willumpie82/ledleafs/CAD/images/0.jpg

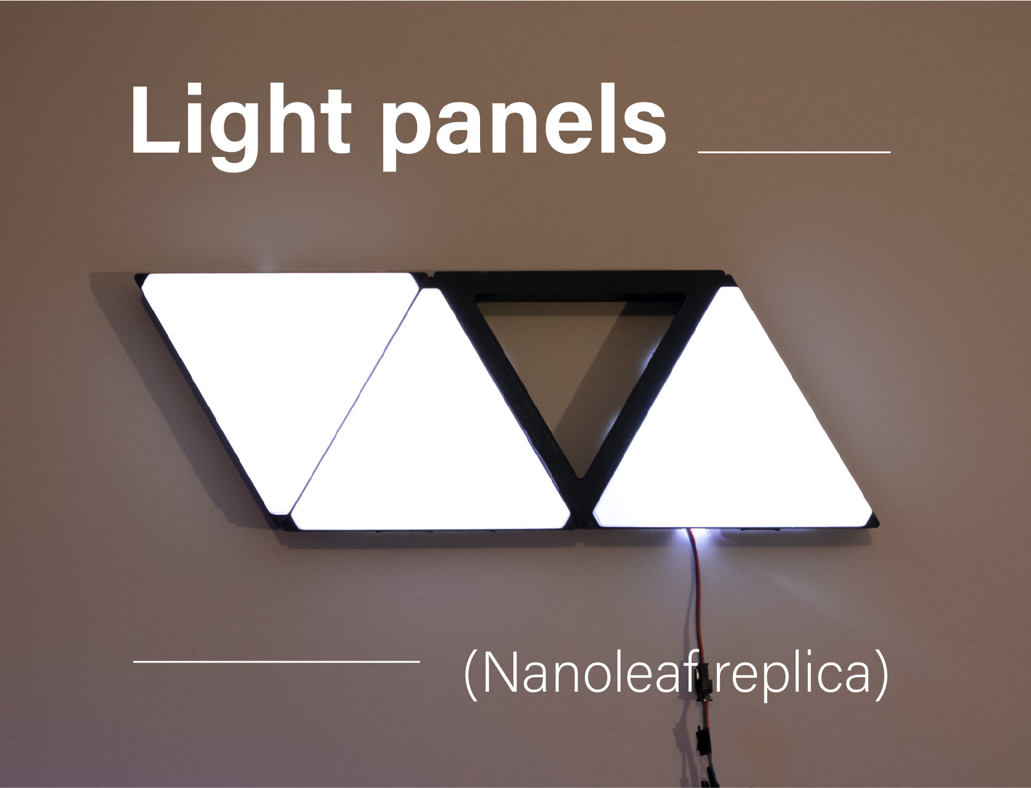
CAD/images/0.jpg
