willumpie82/ledleafs/CAD/images/Manuel_2.jpg

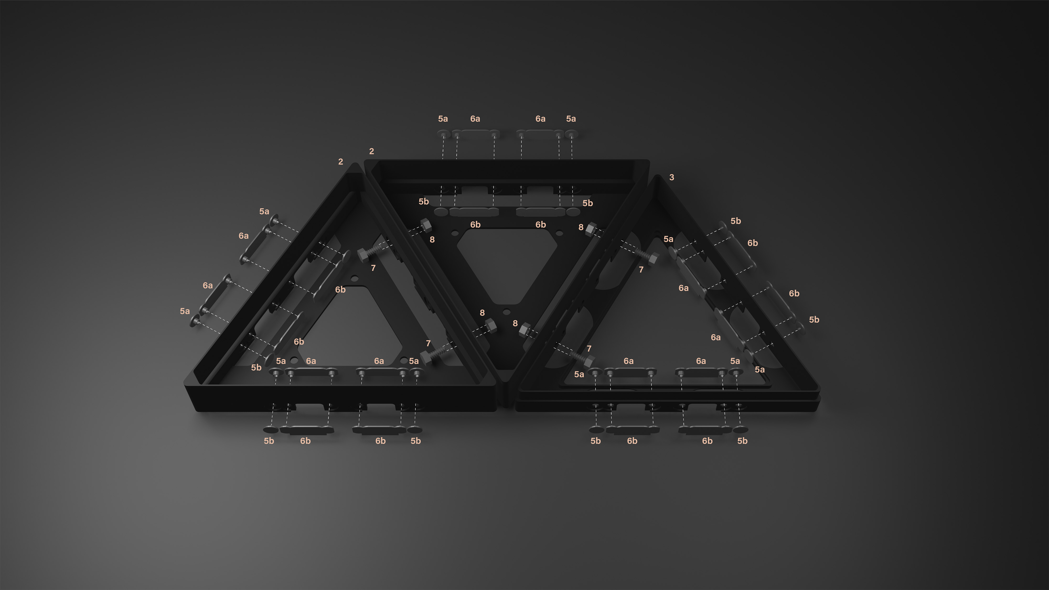
CAD/images/Manuel_2.jpg
