willumpie82/ledleafs/CAD/images/Manuel_5.jpg

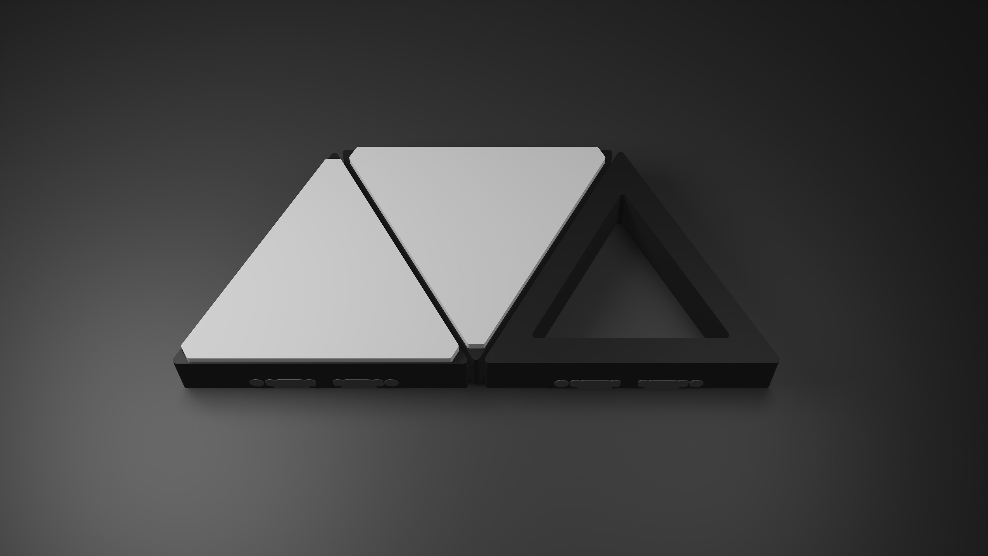
CAD/images/Manuel_5.jpg
