willumpie82/ledleafs/CAD/images/Manuel_6.jpg

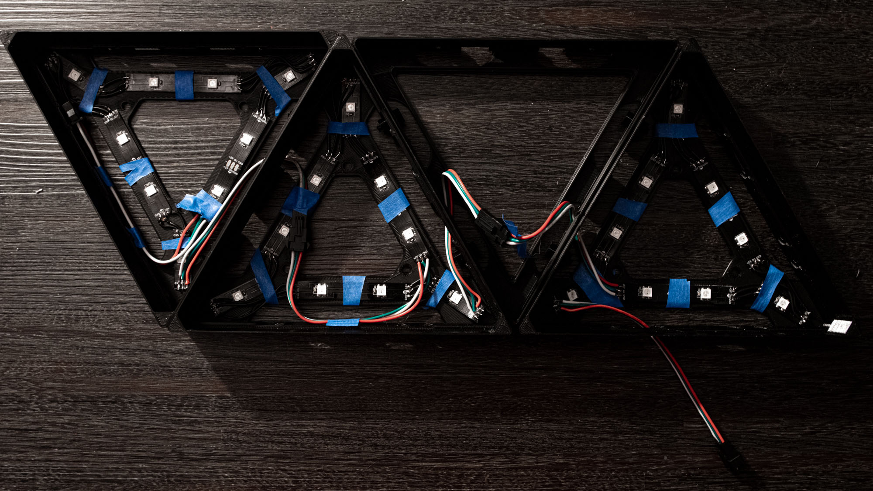
CAD/images/Manuel_6.jpg
