willumpie82/ledleafs/CAD/images/Manuel_8.jpg

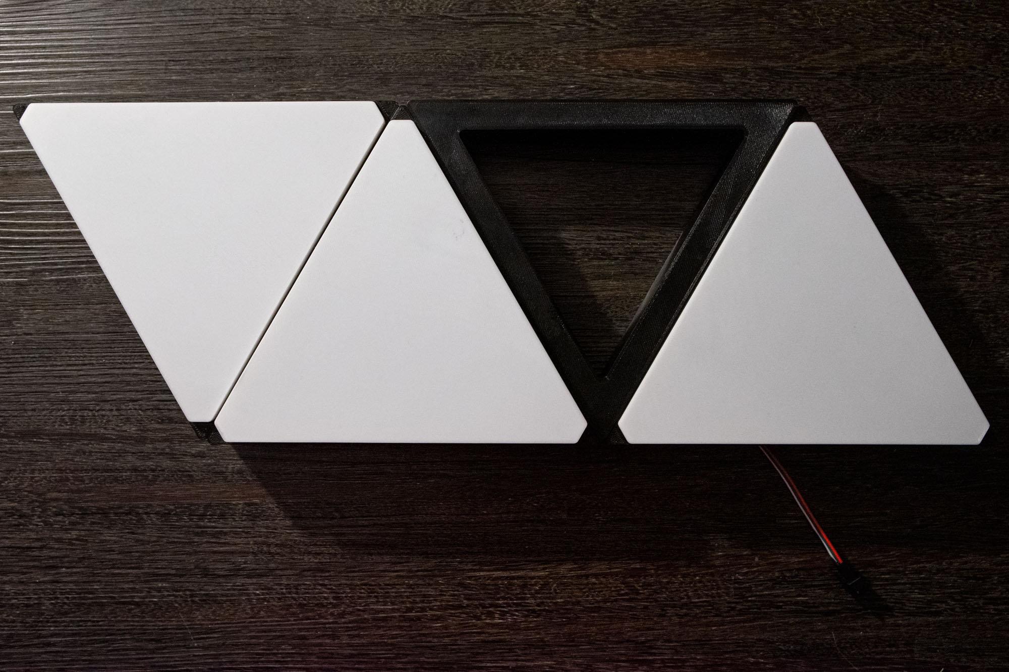
CAD/images/Manuel_8.jpg
