willumpie82/ledleafs/CAD/images/Pres_2.jpg

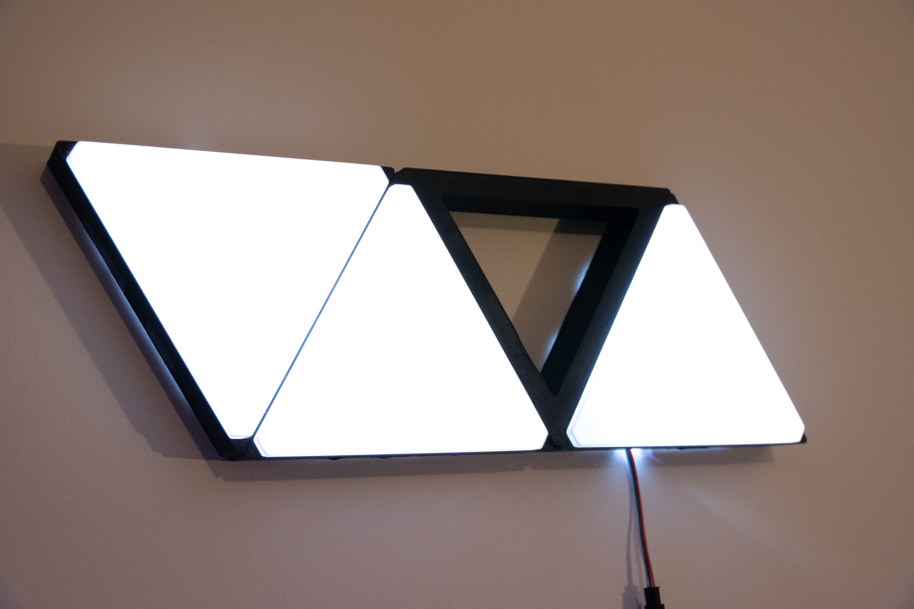
CAD/images/Pres_2.jpg
