willumpie82/ledleafs/CAD/images/snake.jpg

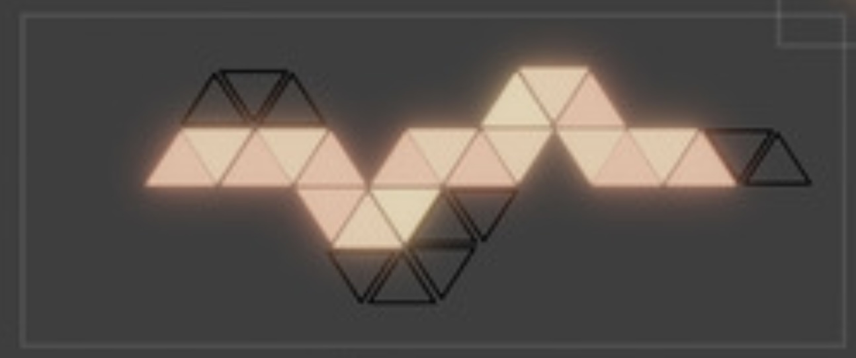
CAD/images/snake.jpg
