willumpie82/ledleafs/SCH/nanoleaf/nanoleaf.jpg

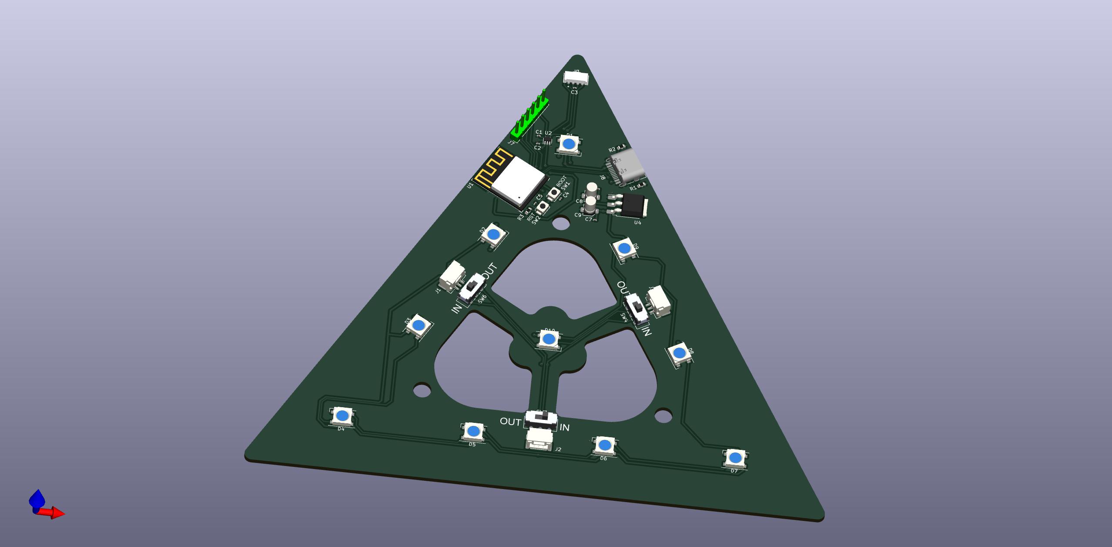
SCH/nanoleaf/nanoleaf.jpg
