willumpie82/ledleafs/CAD/files/1.stl

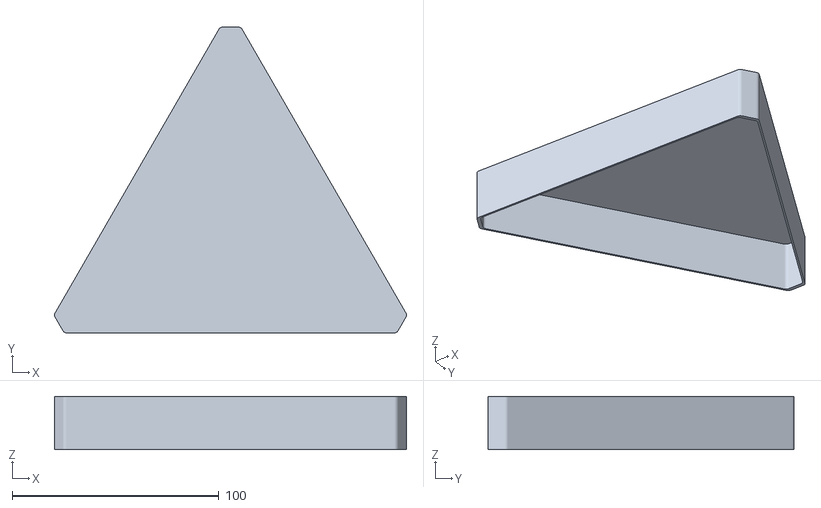
[picture p29: CAD file, 2024-02-09]
CAD/files/1.stl
170.3 x 148.0 x 25.8
