willumpie82/ledleafs/CAD/files/0b.stl

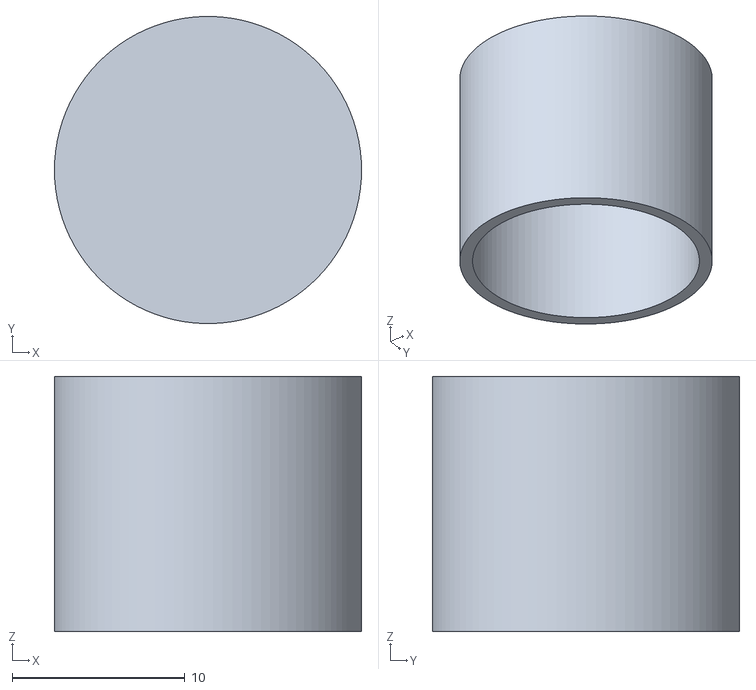
[picture p30: CAD file, 2024-02-09]
CAD/files/0b.stl
17.8 x 17.8 x 14.8
