willumpie82/ledleafs/CAD/files/4.stl

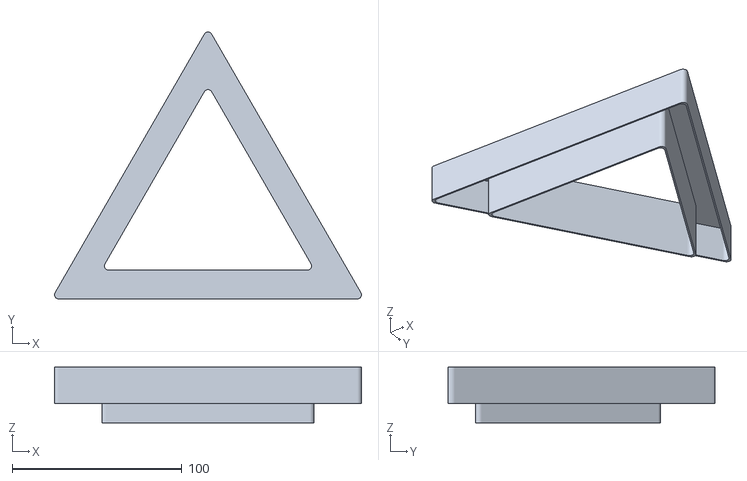
[picture p31: CAD file, 2024-02-09]
CAD/files/4.stl
181.1 x 157.5 x 33.0
